ahsanu123/sudi-keyboard/pcb-design/version_2/output/RedoxV2.png

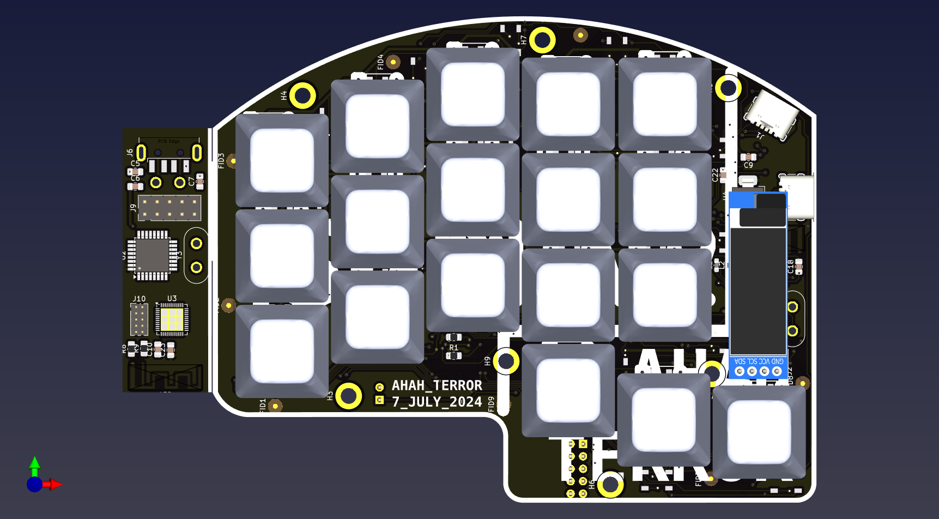
pcb-design/version_2/output/RedoxV2.png
