ahsanu123/sudi-keyboard/pcb-design/version_2/output/sudi-redox-clone-LEFT.png

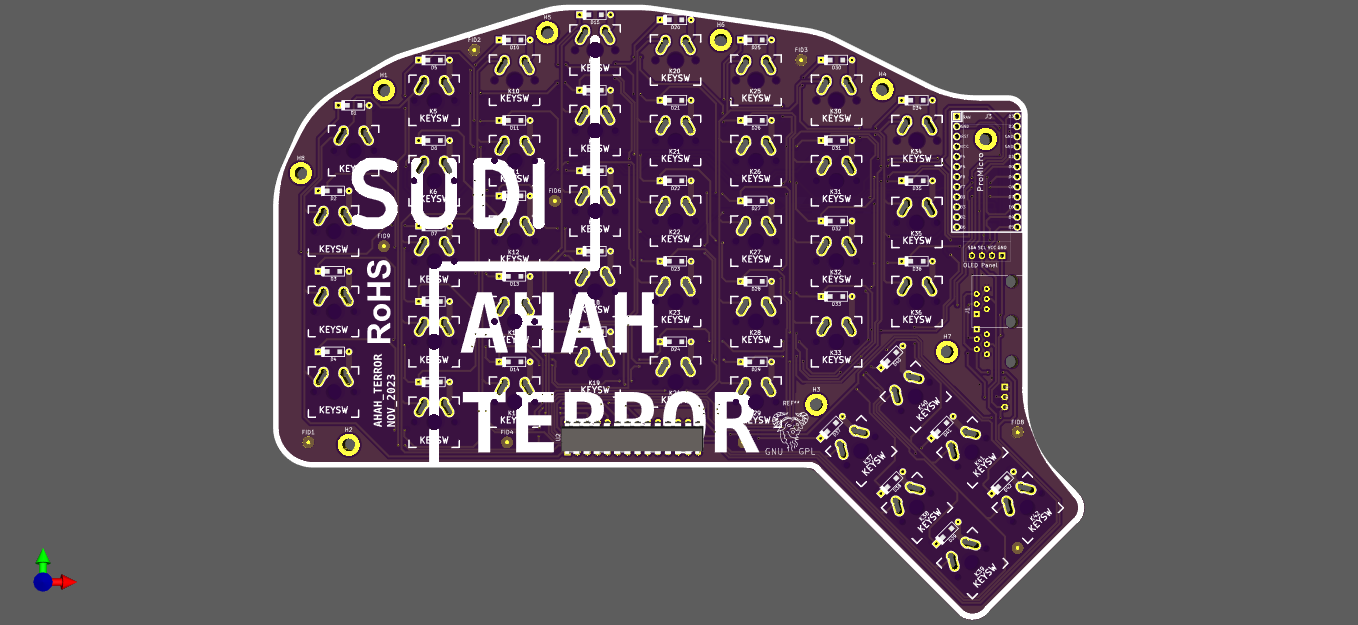
pcb-design/version_2/output/sudi-redox-clone-LEFT.png
