ahsanu123/sudi-keyboard/casing-design/version1/Export/laserCutingV1.pdf

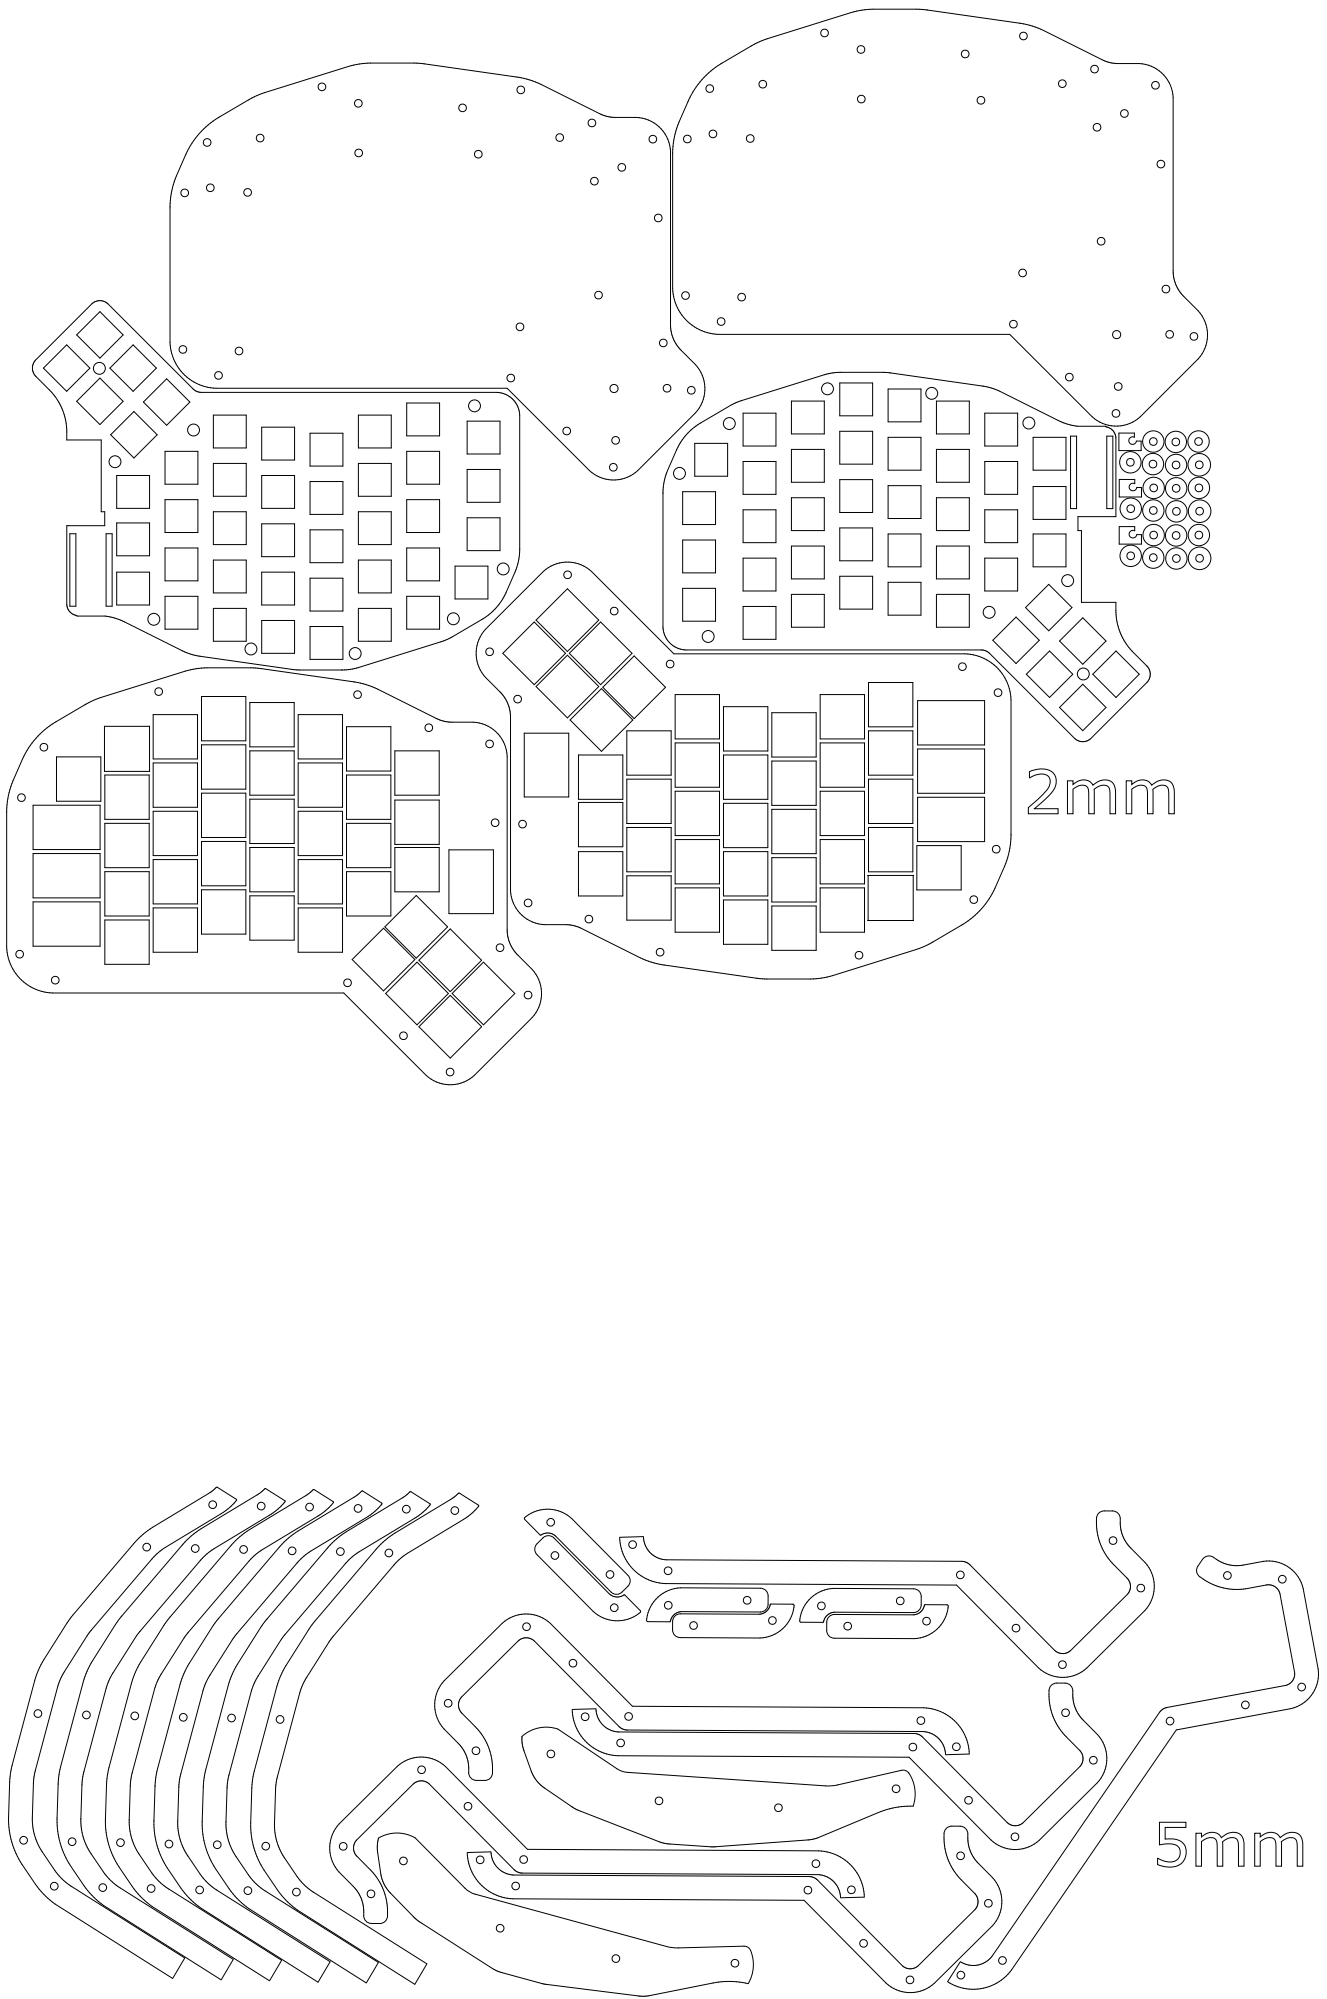
[picture p26: page 1]
