ahsanu123/sudi-keyboard/firmware/v2/src/bin/main.rs

#![no_std]
#![no_main]

use sudi_firmware::info;

use {defmt_rtt as _, panic_probe as _};

use embassy_executor::Spawner;
use embassy_nrf::gpio::{Level, Output, OutputDrive};
use embassy_time::Timer;

#[embassy_executor::main]
async fn main(_spawner: Spawner) {
    let p = embassy_nrf::init(Default::default());
    let mut led = Output::new(p.P0_13, Level::Low, OutputDrive::Standard);

    loop {
        info!("Hello, World!");
        led.set_high();
        Timer::after_millis(500).await;
        led.set_low();
        Timer::after_millis(500).await;
    }
}
